raivo/saab9-5mp3player/images/2016-09-12 14.28.21.jpg

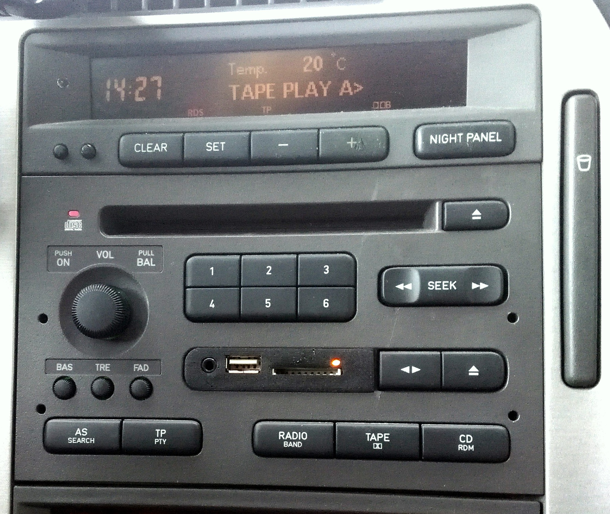
images/2016-09-12 14.28.21.jpg
