raivo/saab9-5mp3player/images/20160216_165024.jpg

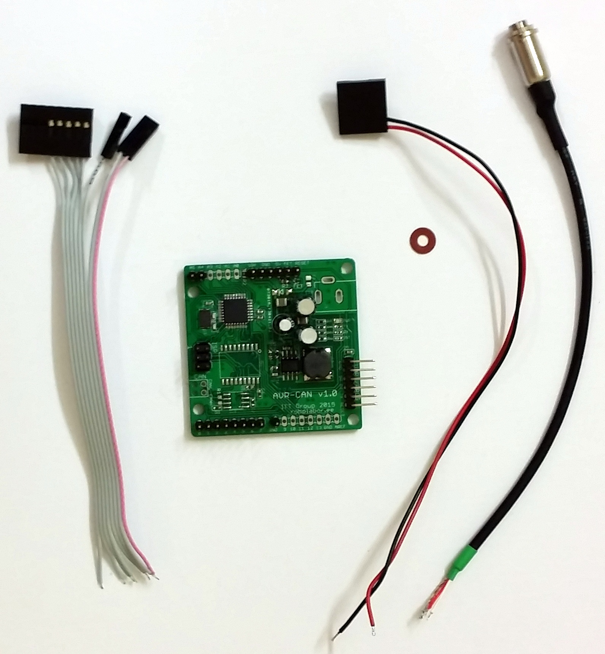
images/20160216_165024.jpg
