raivo/saab9-5mp3player/images/DSCF1494.JPG

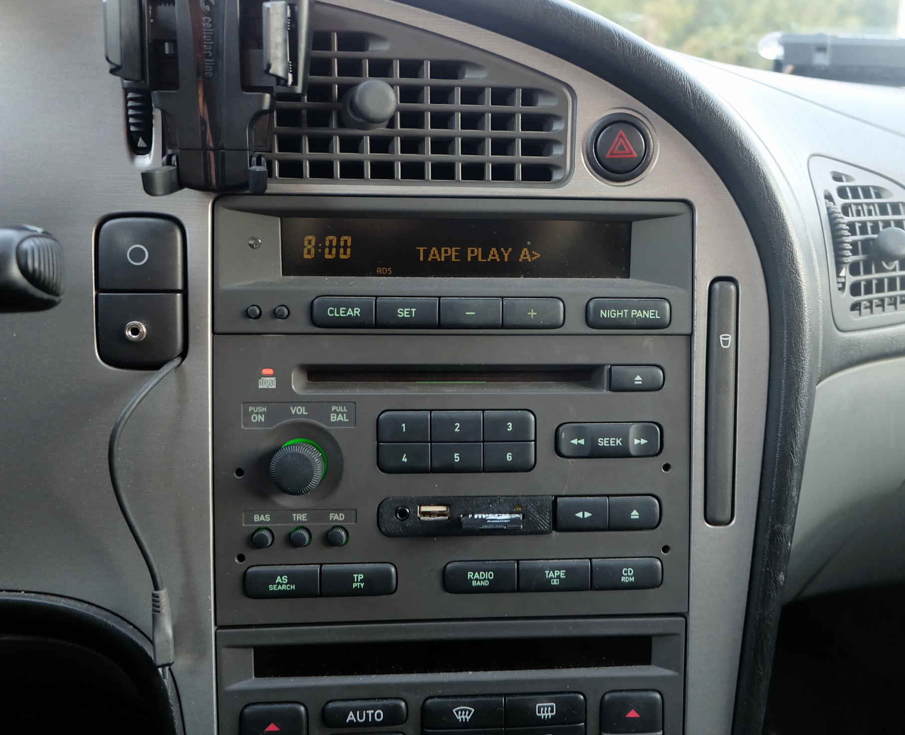
images/DSCF1494.JPG
