raivo/saab9-5mp3player/images/IMG_0594.JPG

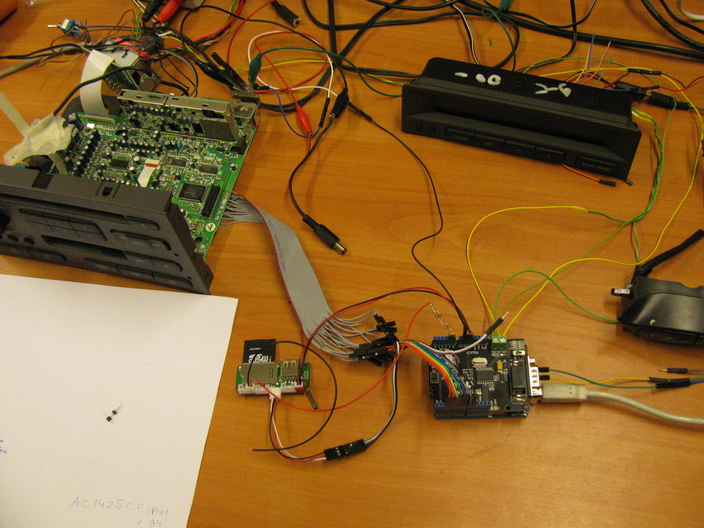
images/IMG_0594.JPG
