raivo/saab9-5mp3player/images/IMG_0595.JPG

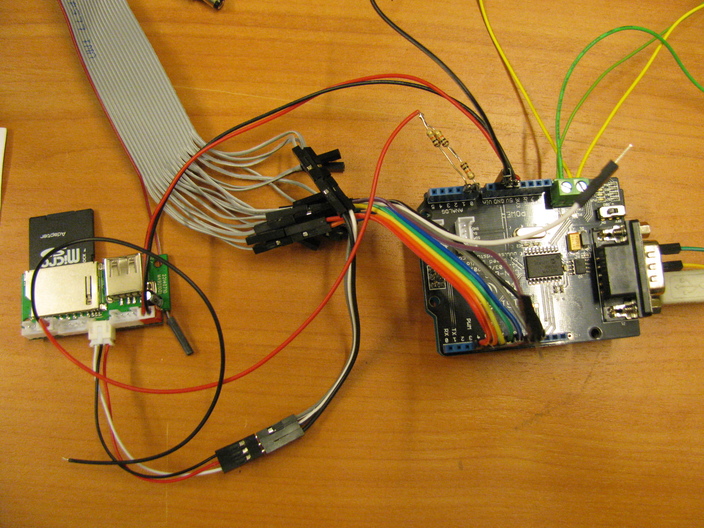
images/IMG_0595.JPG
