raivo/saab9-5mp3player/images/Saab95_tapes_front.JPG

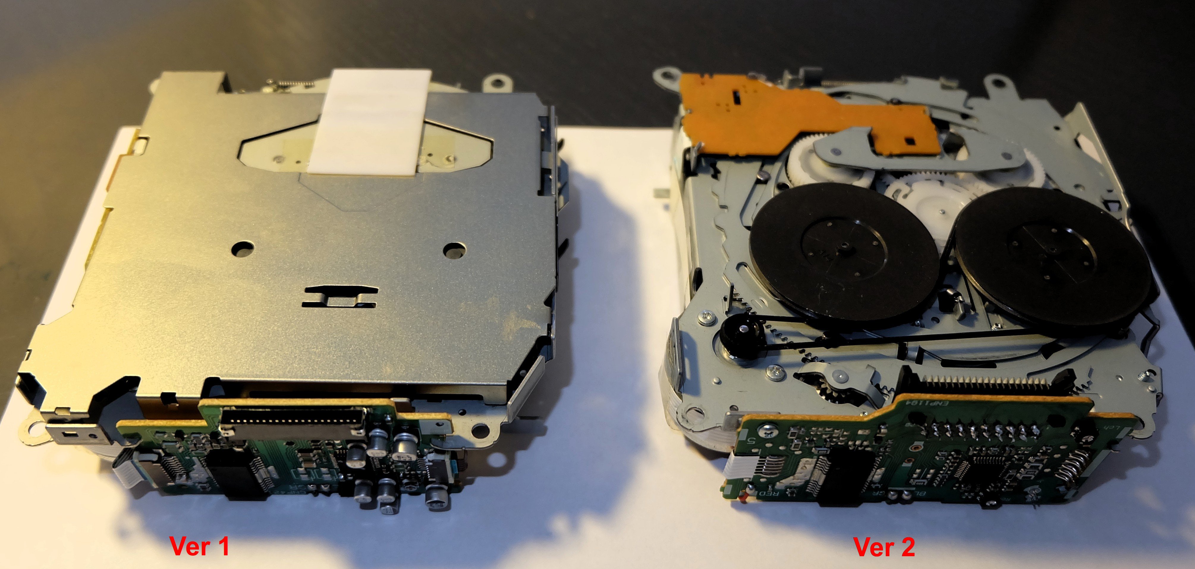
images/Saab95_tapes_front.JPG
