raivo/saab9-5mp3player/images/SID.png

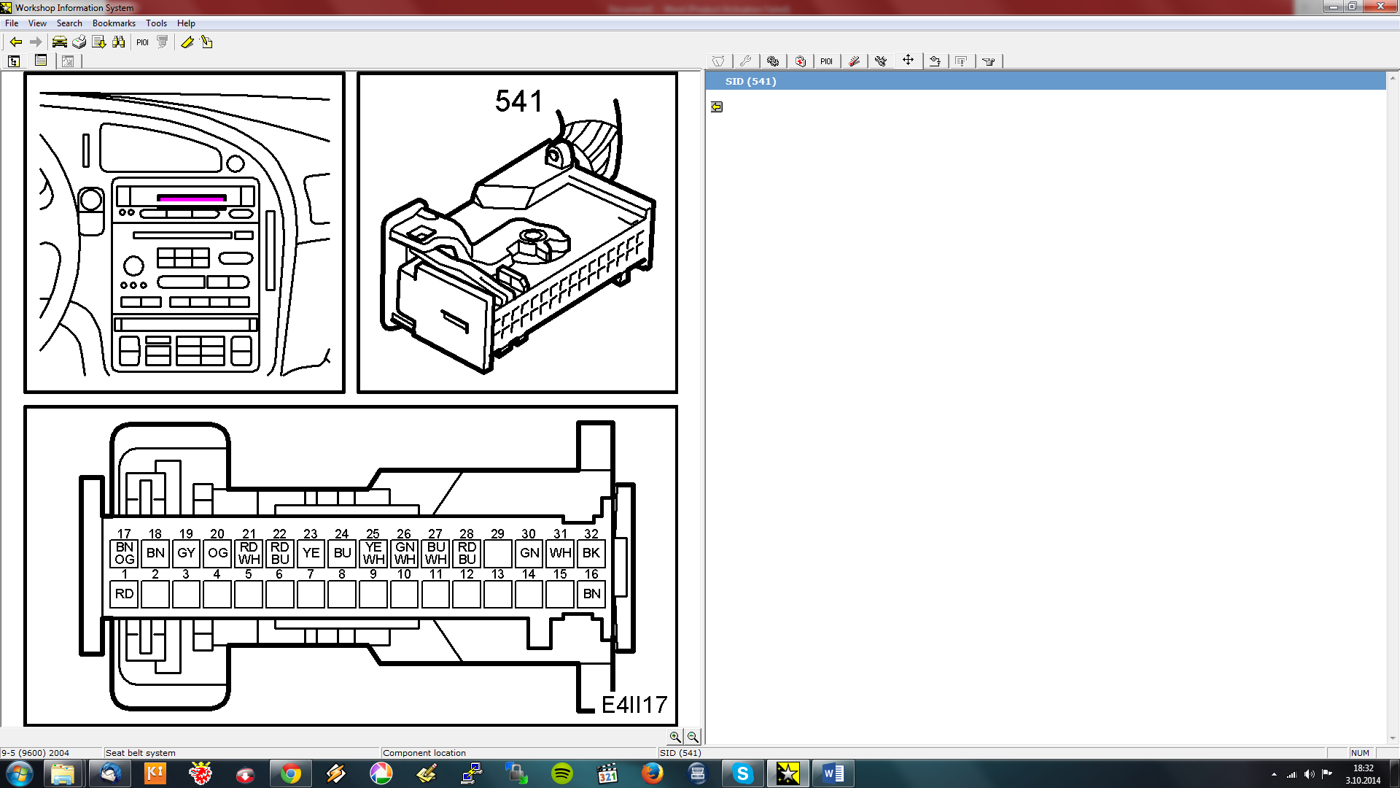
images/SID.png
