raivo/saab9-5mp3player/images/WireHarnessSaab121001.jpg

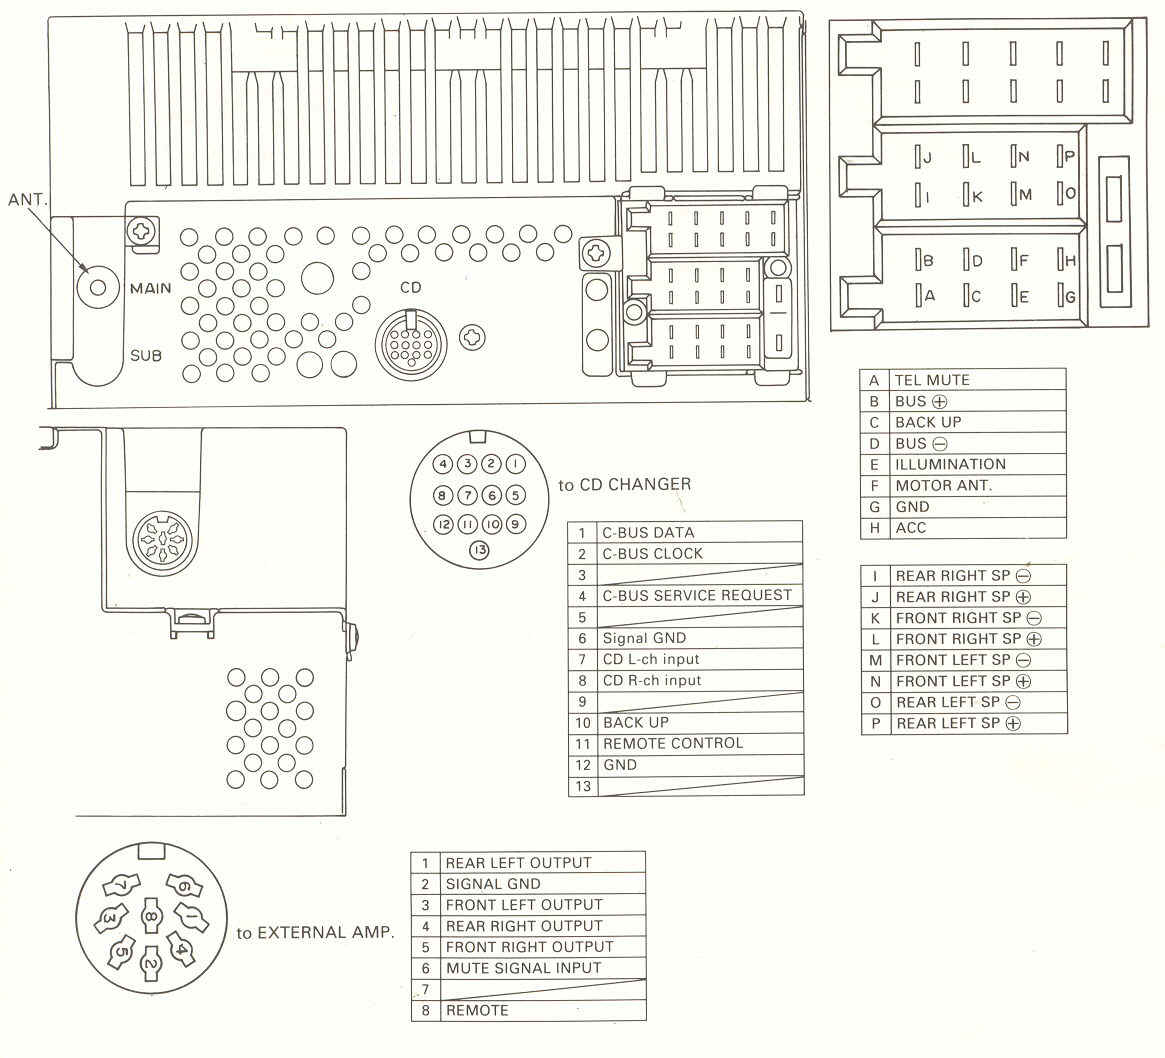
images/WireHarnessSaab121001.jpg
